Liquibit/EnergyTrackingCaMeX-IA/DASH7-firmwares/app/Energy_over_DASH7/network_manager.c

/*
 * Copyright (c) 2015-2021 University of Antwerp, Aloxy NV, LiQuiBit VOF.
 *
 * This file is part of Sub-IoT.
 * See https://github.com/Sub-IoT/Sub-IoT-Stack for further info.
 *
 * Licensed under the Apache License, Version 2.0 (the "License");
 * you may not use this file except in compliance with the License.
 * You may obtain a copy of the License at
 *
 *     http://www.apache.org/licenses/LICENSE-2.0
 *
 * Unless required by applicable law or agreed to in writing, software
 * distributed under the License is distributed on an "AS IS" BASIS,
 * WITHOUT WARRANTIES OR CONDITIONS OF ANY KIND, either express or implied.
 * See the License for the specific language governing permissions and
 * limitations under the License.
 */

/* \file
 *
 *
 * @author contact@liquibit.be
 */
#include <stdio.h>
#include <stdlib.h>
#include <string.h>

#include "hwlcd.h"
#include "hwleds.h"
#include "hwsystem.h"

#include "d7ap_fs.h"
#include "debug.h"
#include "log.h"
#include "scheduler.h"
#include "timer.h"

#include "alp_layer.h"
#include "d7ap.h"
#include "dae.h"

#include "platform.h"

#include "button.h"
#include "led.h"
#include "network_manager.h"

#ifdef FRAMEWORK_NETWORK_MANAGER_LOG
    #define DPRINT(...)      log_print_string(__VA_ARGS__)
    #define DPRINT_DATA(...) log_print_data(__VA_ARGS__)
#else
    #define DPRINT(...)
    #define DPRINT_DATA(...)
#endif

#define CHANNEL_ID 100
#define USE_PUSH7_CHANNEL_SETTINGS false
#define NETWORK_TIMEOUT 10000


static network_state_t network_state = NETWORK_MANAGER_IDLE;
static alp_init_args_t alp_init_args;
static last_transmit_completed_callback transmit_completed_cb;
static uint8_t acked_messages = 0;
static uint8_t nacks_messages = 0;
static uint8_t active_tag_id;


static uint8_t key[]
    = { 0X00, 0X01, 0X02, 0X03, 0X02, 0X01, 0X00, 0X01, 0X02, 0X03, 0X02, 0X01, 0X00, 0X01, 0X02, 0X03 };

// Define the D7 interface configuration used for sending the ALP command on

static alp_interface_config_d7ap_t itf_config = (alp_interface_config_d7ap_t){
  // interface DASH7
  .itf_id = ALP_ITF_ID_D7ASP,
  .d7ap_session_config = {
    .qos = {
        // PREFERRED indicates we first broadcast and then unicast to the closest gateway
        .qos_resp_mode = SESSION_RESP_MODE_PREFERRED,
        // retry modes are not yet implemented
        .qos_retry_mode = SESSION_RETRY_MODE_NO
    },
    // we don't want to start a dormant session but just want to send our data directly
    .dormant_timeout = 0,
    .addressee = {
        .ctrl = {
            // use AES encryption with Counter
            .nls_method = AES_CTR,
            // NBID is a broadcast which expects the amount of receivers present in the id field
            .id_type = ID_TYPE_NBID,
        },
        // use the first subprofile of access profile 0 
        .access_class = 0x01,
        .id = { 3 }
    }
  }
};

static void network_timeout()
{
    // free all commands and let the upper layer know it failed
    alp_layer_free_commands();
    if(transmit_completed_cb)
        transmit_completed_cb(false);
}

/**
 * @brief Callback when a command is completed
 * @param tag_id the id of the command that is completed
 * @param success indicates if the command completed with an error or not
 */
static void on_alp_command_completed_cb(uint8_t tag_id, bool success)
{
    // we're only interested in the command that we triggered ourselves
    if(active_tag_id != tag_id)
        return;
    timer_cancel_task(&network_timeout);
    if (success) {
        DPRINT("Command (%i) completed successfully", tag_id);
    } else {
        DPRINT("Command failed, no ack received");
    }
    if(transmit_completed_cb)
        transmit_completed_cb(success);
}

/**
 * @brief Callback to receive the results
 * @param alp_command The alp_command which triggered this result callback
 * @param origin_itf_status The interface who originally sent the message or who sent an acknowledge on our message
 */
static void on_alp_command_result_cb(alp_command_t* alp_command, alp_interface_status_t* origin_itf_status)
{
    if (origin_itf_status && (origin_itf_status->itf_id == ALP_ITF_ID_D7ASP) && (origin_itf_status->len > 0)) {
        d7ap_session_result_t* d7_result = ((d7ap_session_result_t*)origin_itf_status->itf_status);
        DPRINT("recv response @ %i dB link budget from:", d7_result->rx_level);
    }
    network_state = NETWORK_MANAGER_READY;
}

/**
 * @brief Transmit a file over the configured network
 * @param file_id the id of the file we're trying to send
 * @param offset the offset inside the file we're trying to send
 * @param length the length of the data inside the file we're trying to send
 * @param data a pointer to the data inside the file we're trying to send
 * @return error_t
 */
error_t transmit_file(uint8_t file_id, uint32_t offset, uint32_t length, uint8_t *data)
{
    bool ret;
    if(network_state != NETWORK_MANAGER_READY)
        return EBUSY;
    // Generate ALP command.
    // We will be sending a return file data action, without a preceding file read request.
    // This is an unsolicited message, where we push the sensor data to the gateway(s).

    // alloc command. This will be freed when the command completes
    alp_command_t* command = alp_layer_command_alloc(true, true); 
    // forward to the D7 interface
    ret = alp_append_forward_action(command, (alp_interface_config_t*)&itf_config, d7ap_session_config_length(&itf_config.d7ap_session_config)); 
    // add the return file data action
    ret = alp_append_return_file_data_action(command, file_id, offset, length, data); 
    // and finally execute this
    active_tag_id = command->tag_id;
    alp_layer_process(command); 
    network_state = NETWORK_MANAGER_TRANSMITTING;
    timer_post_task_delay(&network_timeout, NETWORK_TIMEOUT);
    return SUCCESS;
}

/**
 * @brief The network quality is indicated by how many times we tried to send a message compared to how many times we successfully sent it
 * @param acks The total amount of acknowledges we got
 * @param nacks The total amount of times we failed to send a message
 */
void get_network_quality(uint8_t* acks, uint8_t* nacks)
{
    acks = &acked_messages;
    nacks = &nacks_messages;
}

network_state_t get_network_manager_state()
{
    return network_state;
}

/**
 * @brief Initializes the network configuration, also initializing the operating system itself
 * @param last_transmit_completed_cb a callback which is called when a file got transmitted with or without error
 */
void network_manager_init(last_transmit_completed_callback last_transmit_completed_cb)
{
    // initialize the filesystem, operating system and network stacks
    alp_init_args.alp_command_completed_cb = &on_alp_command_completed_cb;
    alp_init_args.alp_command_result_cb = &on_alp_command_result_cb;
    alp_layer_init(&alp_init_args, false);


    transmit_completed_cb = last_transmit_completed_cb;
    sched_register_task(&network_timeout);

    // write some custom channel settings. This can also be done directly in d7ap_fs_data.c
    if (USE_PUSH7_CHANNEL_SETTINGS) { //TODO check why this doesn't work
        dae_access_profile_t push7_access_profile;
        d7ap_fs_read_access_class(0, &push7_access_profile);

        push7_access_profile.subbands[0].channel_index_start = CHANNEL_ID;
        push7_access_profile.subbands[0].channel_index_end = CHANNEL_ID;
        push7_access_profile.subbands[0].eirp = 5;
        push7_access_profile.subbands[1].channel_index_start = CHANNEL_ID;
        push7_access_profile.subbands[1].channel_index_end = CHANNEL_ID;
        push7_access_profile.subbands[1].eirp = 0;

        d7ap_fs_write_access_class(0, &push7_access_profile);

        uint32_t length = D7A_FILE_NWL_SECURITY_KEY_SIZE;
        d7ap_fs_write_file(D7A_FILE_NWL_SECURITY_KEY, 0, key, length, ROOT_AUTH);
    }
    // indicate everything is initialized and ready to transmit
    network_state = NETWORK_MANAGER_READY;
}

/**
 * @brief set a custom tx power to increase range or to increase battery life
 * @param tx_power a number indicating the power the device will be sending at. This should be a number between 0 and 20 (dB)
 */
void network_manager_set_tx_power(uint8_t tx_power)
{
    // we are sending all our messages on access class 0. Changing the output power is done by writing a new 'eirp' value to that access class
    dae_access_profile_t push7_access_profile;
    d7ap_fs_read_access_class(0, &push7_access_profile);
    push7_access_profile.subbands[0].eirp = tx_power;
    d7ap_fs_write_access_class(0, &push7_access_profile);
}
